andrefs/sonotify-nfc-esp32/main/wifi.c

#include "wifi.h"

#include "esp_event.h"
#include "esp_log.h"
#include "esp_netif.h"
#include "esp_wifi.h"
#include "freertos/FreeRTOS.h"
#include "freertos/event_groups.h"
#include "freertos/task.h"

#include "led.h"

static const char *TAG = "wifi";

#define WIFI_SSID CONFIG_WIFI_SSID
#define WIFI_PASS CONFIG_WIFI_PASSWORD
#define MAX_RETRY CONFIG_WIFI_MAX_RETRY

static EventGroupHandle_t s_wifi_event_group;
#define WIFI_CONNECTED_BIT BIT0
#define WIFI_FAIL_BIT BIT1
static int s_retry_num = 0;

static void wifi_event_handler(void *arg, esp_event_base_t event_base,
                               int32_t event_id, void *event_data) {
  if (event_base == WIFI_EVENT && event_id == WIFI_EVENT_STA_START) {
    led_set_blink_mode(LED_BLINK_SLOW); // Wi-Fi connecting
    esp_wifi_connect();
  } else if (event_base == WIFI_EVENT &&
             event_id == WIFI_EVENT_STA_DISCONNECTED) {
    if (s_retry_num < MAX_RETRY) {
      led_set_blink_mode(LED_BLINK_SLOW); // still connecting
      esp_wifi_connect();
      s_retry_num++;
      ESP_LOGI(TAG, "Retrying connection...");
    } else {
      led_set_blink_mode(LED_BLINK_FAST); // Wi-Fi failed
      xEventGroupSetBits(s_wifi_event_group, WIFI_FAIL_BIT);
    }
  } else if (event_base == IP_EVENT && event_id == IP_EVENT_STA_GOT_IP) {
    led_set_blink_mode(LED_BLINK_OFF); // connected
    ip_event_got_ip_t *event = (ip_event_got_ip_t *)event_data;
    ESP_LOGI(TAG, "Got IP:" IPSTR, IP2STR(&event->ip_info.ip));
    s_retry_num = 0;
    xEventGroupSetBits(s_wifi_event_group, WIFI_CONNECTED_BIT);
  }
}

void wifi_init(void) {
  esp_netif_create_default_wifi_sta();

  wifi_init_config_t cfg = WIFI_INIT_CONFIG_DEFAULT();
  ESP_ERROR_CHECK(esp_wifi_init(&cfg));

  esp_event_handler_instance_t instance_any_id;
  esp_event_handler_instance_t instance_got_ip;

  ESP_ERROR_CHECK(esp_event_handler_instance_register(
      WIFI_EVENT, ESP_EVENT_ANY_ID, &wifi_event_handler, NULL,
      &instance_any_id));
  ESP_ERROR_CHECK(esp_event_handler_instance_register(
      IP_EVENT, IP_EVENT_STA_GOT_IP, &wifi_event_handler, NULL,
      &instance_got_ip));

  wifi_config_t wifi_config = {
      .sta =
          {
              .ssid = WIFI_SSID,
              .password = WIFI_PASS,
              .threshold.authmode = WIFI_AUTH_WPA2_PSK,
          },
  };

  ESP_ERROR_CHECK(esp_wifi_set_mode(WIFI_MODE_STA));
  ESP_ERROR_CHECK(esp_wifi_set_config(WIFI_IF_STA, &wifi_config));
  ESP_ERROR_CHECK(esp_wifi_start());

  ESP_LOGI(TAG, "Wi-Fi initialization finished.");

  s_wifi_event_group = xEventGroupCreate();
  EventBits_t bits = xEventGroupWaitBits(
      s_wifi_event_group, WIFI_CONNECTED_BIT | WIFI_FAIL_BIT, pdFALSE, pdFALSE,
      pdMS_TO_TICKS(10000) // wait up to 10 seconds
  );

  if (bits & WIFI_CONNECTED_BIT) {
    ESP_LOGI(TAG, "Connected to SSID:%s", WIFI_SSID);
  } else if (bits & WIFI_FAIL_BIT) {
    ESP_LOGI(TAG, "Failed to connect to SSID:%s", WIFI_SSID);
  } else {
    ESP_LOGI(TAG, "Wi-Fi connection timed out");
  }
}
